skarnik5742/Fiber_Project/pytest_blink.py

# SPDX-FileCopyrightText: 2022-2025 Espressif Systems (Shanghai) CO LTD
# SPDX-License-Identifier: CC0-1.0
import logging
import os

import pytest
from pytest_embedded_idf.dut import IdfDut
from pytest_embedded_idf.utils import idf_parametrize


@pytest.mark.generic
@idf_parametrize('target', ['supported_targets'], indirect=['target'])
def test_blink(dut: IdfDut) -> None:
    # check and log bin size
    binary_file = os.path.join(dut.app.binary_path, 'blink.bin')
    bin_size = os.path.getsize(binary_file)
    logging.info('blink_bin_size : {}KB'.format(bin_size // 1024))
